nielsverhoeven/PoE-FanController/.github/agents/feature.breakdown.agent.md

---
name: feature.breakdown
description: >
  Breaks an approved feature plan into dependency-ordered tasks and creates or
  updates GitHub issues for each task. Maintains a tasks.md file as the local
  task register. Use when asked to "break down a feature", "create tasks", "generate
  task list", or when the orchestrator delegates Stage 4 of the feature pipeline.
tools:
  - read
  - edit
  - search
  - shell
handoffs:
  - label: Start Implementation
    agent: implementer
    prompt: Task breakdown is complete. Implement tasks in dependency order.
    send: false
  - label: Return to Orchestrator
    agent: orchestrator
    prompt: Task breakdown complete. Resume the pipeline at Stage 5 (Implementation).
    send: false
  - label: Update Issues
    agent: github.issues-manager
    prompt: Create or update GitHub issues for the tasks in this breakdown and write issue numbers back into tasks.md.
    send: false
---

# Feature Breakdown Agent

You convert an approved feature plan into a dependency-ordered task list and create corresponding GitHub issues, so implementation can proceed in the right order with every task tracked.

---

## Inputs

1. `docs/features/<feature-name>/spec.md` — requirements and success criteria
2. `docs/features/<feature-name>/plan.md` — technical approach
3. `docs/constitution.md` — mandatory task categories (testing, documentation, etc.)
4. `docs/architecture.md` — hardware block diagram and firmware module structure
5. Parent feature issue number — the existing feature issue that must own all task child issues

---

## Task Generation Rules

### Task Structure
Each task must have:
- **ID**: `T###` (zero-padded, e.g. T001)
- **Title**: action-noun format ("Add temperature sensor I2C driver")
- **Description**: what to do, in which file/module, and why
- **Layer**: which layer (see below)
- **Dependencies**: which T### IDs must be complete first
- **Acceptance**: one-line verifiable done condition

### Task Layers (mandatory coverage for every feature that touches that area)
| Layer | When required |
|---|---|
| **Hardware: Schematic** | Any new component, net, or symbol change in KiCad |
| **Hardware: ERC** | After every schematic task |
| **Hardware: Layout** | Any new component placement or routing change |
| **Hardware: DRC** | After every layout task |
| **Hardware: BOM** | Any new component added |
| **Firmware: Module** | New or modified C/C++ source module |
| **Firmware: Config** | New configuration parameter in config.h |
| **Web UI** | New REST endpoint or UI page/control |
| **Unit Tests** | For every new firmware module or function |
| **Documentation** | Spec updates, architecture diagram updates, guide updates |
| **Issue update** | Final status update to GitHub issue |

Not every feature touches every layer. Only include layers that are genuinely needed.

### Dependency Ordering
Build a dependency graph. Tasks with no dependencies are "ready" immediately.

Example for a temperature sensor feature:
```
T001 (Schematic: add sensor symbol) -> T002 (ERC) -> T003 (Layout: place + route) -> T004 (DRC)
T004 -> T005 (Firmware: I2C driver module) -> T006 (Firmware: unit tests)
T005 -> T007 (Web UI: temperature display endpoint)
T006, T007 -> T008 (Documentation)
T008 -> T009 (Issue update)
```

---

## Output: `tasks.md`

Create `docs/features/<feature-name>/tasks.md`:

```markdown
# Tasks: <Feature Name>

## Summary
- Total tasks: N
- Layers covered: [list]
- GitHub issue: #<number>

## Dependency Graph
[mermaid or text graph]

## Task List

### T001: <Title>
- **Layer**: <layer>
- **Description**: <what, where, why>
- **Depends on**: none
- **Acceptance**: <done condition>
- **GitHub issue**: #<issue number> (filled by github.issues-manager)

### T002: <Title>
...
```

---

## GitHub Issue Creation

After generating `tasks.md`, delegate to `github.issues-manager`:
- Create one GitHub issue per task (label: `task`)
- Use the existing feature issue as the parent issue (do not create a replacement parent issue when one already exists)
- Write issue numbers back into `tasks.md`
- Link task issues as sub-issues of the parent feature issue
- If a task issue is linked to the wrong parent, request hierarchy repair via `github.issues-manager` before implementation starts

---

## Constraints

- Every task must be independently verifiable (a reviewer can mark it done without knowing other tasks).
- No task may span multiple layers — split if needed.
- ERC and DRC tasks are mandatory after any schematic or layout change respectively.
- Always include unit test and documentation tasks — they are not optional.
- Never create tasks that violate `docs/constitution.md` principles.
- Never invert issue hierarchy: feature issue is parent; task issues are children.
