nielsverhoeven/PoE-FanController/docs/kb/ESP32-P4-POE-ETH/pin-layout.md

# ESP32-P4-ETH Dev Board — Pin Layout Reference

**Board**: Waveshare ESP32-P4-ETH  
**Source**: Board silkscreen image `ESP32-P4-ETH-details-inter-d78f8087f1a1597badd3a1d077c4c057.webp`  
**Verified by user**: Pin 1 = DP/GPIO25, Pin 21 = GPIO48, Pin 3 = GND, Pin 23 = GND

## CRITICAL: Pin Numbering Convention

The board uses a **consecutive (non-Pico) pin layout**:

```
LEFT COLUMN:  Pin  1 (bottom-left)  →  Pin 20 (top-left)
RIGHT COLUMN: Pin 21 (bottom-right) →  Pin 40 (top-right)
```

**Never use Pico-style (dual-row interleaved) numbering for this board.**

### KiCad schematic symbol orientation

The `Custom:J8_Waveshare` symbol in the schematic is oriented to **match the physical board**:
- `pins_right` list runs **40 → 21** (top-to-bottom in symbol) so pin 40 (VBUS) appears at the **top-right** and pin 21 (GPIO48) at the **bottom-right**
- `pins_left` list runs **20 → 1** (top-to-bottom in symbol) so pin 20 (GPIO54) appears at the **top-left** and pin 1 (DP/GPIO25) at the **bottom-left**

This matches the physical Waveshare board where VBUS is at the top-right corner and GPIO48 is at the bottom-right corner.

---

## Left Column — Pins 1–20

| Pin | Signal | Type | Notes |
|-----|---|---|---|
|  1  | DP / GPIO25 | GPIO | USB D+ / General IO |
|  2  | DM / GPIO24 | GPIO | USB D- / General IO |
|  3  | GND | Ground | |
|  4  | SDA / GPIO7 | GPIO | I²C Data |
|  5  | SCL / GPIO8 | GPIO | I²C Clock |
|  6  | GPIO2 | GPIO | |
|  7  | GPIO3 | GPIO | |
|  8  | GND | Ground | |
|  9  | GPIO4 | GPIO | |
| 10  | GPIO5 | GPIO | |
| 11  | GPIO6 | GPIO | |
| 12  | GPIO14 | GPIO | |
| 13  | GND | Ground | |
| 14  | GPIO15 | GPIO | |
| 15  | GPIO16 | GPIO | |
| 16  | GPIO17 | GPIO | |
| 17  | GPIO18 | GPIO | |
| 18  | GND | Ground | |
| 19  | GPIO19 | GPIO | |
| 20  | GPIO54 | GPIO | |

---

## Right Column — Pins 21–40

| Pin | Signal | Type | Notes |
|-----|---|---|---|
| 21  | GPIO48 | GPIO | |
| 22  | GPIO47 | GPIO | |
| 23  | GND | Ground | |
| 24  | GPIO46 | GPIO | |
| 25  | GPIO33 | GPIO | |
| 26  | GPIO32 | GPIO | |
| 27  | GPIO27 | GPIO | |
| 28  | GND | Ground | |
| 29  | GPIO26 | GPIO | |
| 30  | RUN | System Control | Chip enable / run control |
| 31  | GPIO23 | GPIO | |
| 32  | GPIO22 | GPIO | |
| 33  | GND | Ground | |
| 34  | GPIO21 | GPIO | |
| 35  | GPIO20 | GPIO | |
| 36  | 3V3 | Power | 3.3 V output |
| 37  | EN | System Control | Module enable |
| 38  | GND | Ground | |
| 39  | VSYS | Power | System voltage input |
| 40  | VBUS | Power | USB 5 V — **use for 5 V supply** |

---

## Additional Connectors

### USB-C (top of board, labelled on silkscreen)
| Label | Signal |
|---|---|
| D- | USB D- |
| VCC | Power  |
| D+ | USB D+ |
| GND | Ground |

### PoE / ETH Pads (bottom of board)
| Side  | Label | Type | Notes |
|---|---|---|---|
| Left  | GND | Ground | |
| Left  | VCC | Power | |
| Left  | RJ12  | ETH POE  | PoE rail |
| Right | RJ78  | ETH POE  | PoE rail |
| Right | RJ45  | ETH POE  | PoE rail |
| Right | RJ36  | ETH POE  | PoE rail |

---

## Power Supply Notes

- **5 V supply → use Pin 40 (VBUS)**, not Pin 39 (VSYS).  
  VBUS is the USB 5 V bus rail and is the correct source for regulated 5 V.  
  VSYS is the system input rail and should not be used as a 5 V supply source.
- **3.3 V output → Pin 36 (3V3)**. Do not use this as a power input.
- GND pins: 3, 8, 13, 18, 23, 28, 33, 38 (8 total across both columns).

---

## Pin Type Legend

| Colour in image | Meaning |
|---|---|
| Green | GPIO |
| Black | Ground |
| Red | Power |
| Pink | System Control |
| Yellow | ETH POE |

---

## Daughter Board Signal Assignments (PoE FanController PCB)

### Right Column (Pins 21–40) — Fan + Power signals

| Pin | GPIO | Signal | Direction | Connected to |
|-----|---|---|---|---|
| 21  | GPIO48 | **FAN4_PWM**  | Output | J5 pin 4, via D5/R12 PWM LED |
| 22  | GPIO47 | **FAN4_TACH** | Input  | R8 TACH pull-up (10kΩ to +3V3) |
| 23  | GND | GND | — | — |
| 24  | GPIO46 | **FAN3_PWM**  | Output | J4 pin 4, via D4/R11 PWM LED |
| 25  | GPIO33 | **FAN3_TACH** | Input  | R7 TACH pull-up (10kΩ to +3V3) |
| 26  | GPIO32 | NC | — | EMAC_RXD0 — do not use |
| 27  | GPIO27 | NC | — | — |
| 28  | GND | GND | — | — |
| 29  | GPIO26 | NC | — | — |
| 30  | RUN | NC | — | System control — reserved |
| 31  | GPIO23 | **FAN2_PWM**  | Output | J3 pin 4, via D3/R10 PWM LED |
| 32  | GPIO22 | **FAN2_TACH** | Input  | R6 TACH pull-up (10kΩ to +3V3) |
| 33  | GND | GND | — | — |
| 34  | GPIO21 | **FAN1_PWM**  | Output | J2 pin 4, via D2/R9 PWM LED |
| 35  | GPIO20 | **FAN1_TACH** | Input  | R5 TACH pull-up (10kΩ to +3V3) |
| 36  | +3V3 | **+3V3** | Power  | TACH pull-ups R5-R8, sensor VCC |
| 37  | EN | NC | — | Module enable — reserved |
| 38  | GND | GND | — | — |
| 39  | VSYS | NC | — | Do NOT use for 5V supply |
| 40  | VBUS | **+5V** | Power  | U_BOOST IN+ (5V→12V boost input) |

> ⚠️ PWM and TACH are on **adjacent pins per fan** — PWM on the lower-numbered pin, TACH on the higher. This is the result of a board layout reshuffle (2026-06-14) that required swapping from the original TACH-low/PWM-high order.

### Left Column (Pins 1–20) — Sensor + LED signals

| Pin | GPIO | Signal | Direction | Connected to |
|-----|---|---|---|---|
| 6 | GPIO2  | DS18B20_DATA | Bidirectional | R14 pull-up (4.7kΩ to +3V3), J6 |
| 10  | GPIO5  | DHT11_DATA | Input | HUM1 pin 2 |
| 11  | GPIO6  | PROBE_LED | Output | R15 → LED6 |
| 16  | GPIO17 | PROG_LED | Output | R13 → LED2 |
| 17  | GPIO18 | PWR_LED | Output | R3 → LED1 |
| 3,8,13,18 | GND | GND | — | — |

### PCB Component Positions (as-built, 2026-06-15 — fully routed)

Board outline: **92mm × 78mm** (X: 12–104mm, Y: 12–90mm) with rounded corners.
All signal components on F.Cu. Wire jumpers JP1–JP4 on B.Cu.
Routing: single layer F.Cu, **0.4mm** track width, 242 segments.
**DRC: 0 errors, 0 unconnected, 7 warnings (cosmetic only).**

| Ref | X (mm) | Y (mm) | Rotation | Layer | Role |
|-----|---|---|---|---|---|
| **J8** | **41.000** | **40.770** | **90°** | F.Cu | ESP32-P4-PoE-ETH interface header |
| U_BOOST | 77.000 | 25.140 | 0° | F.Cu | DC-DC boost module (LM2587, 5V→12V) |
| J2 | 96.500 | 46.500 | 180° | F.Cu | FAN1 header (Molex KK-254 4-pin) |
| J3 | 96.500 | 58.500 | 180° | F.Cu | FAN2 header |
| J4 | 96.500 | 70.500 | 180° | F.Cu | FAN3 header |
| J5 | 96.500 | 82.500 | 180° | F.Cu | FAN4 header |
| R5 | 65.000 | 47.770 | 90° | F.Cu | FAN1 TACH pull-up (10kΩ, pin 35/GPIO20) |
| R6 | 65.000 | 60.450 | 90° | F.Cu | FAN2 TACH pull-up (10kΩ, pin 32/GPIO22) |
| R7 | 65.000 | 73.130 | 90° | F.Cu | FAN3 TACH pull-up (10kΩ, pin 25/GPIO33) |
| R8 | 65.000 | 85.810 | 90° | F.Cu | FAN4 TACH pull-up (10kΩ, pin 22/GPIO47) |
| R9 | 69.000 | 40.150 | -90° | F.Cu | FAN1 PWM LED resistor (150Ω) |
| R10 | 69.000 | 52.830 | -90° | F.Cu | FAN2 PWM LED resistor (150Ω) |
| R11 | 69.000 | 65.510 | -90° | F.Cu | FAN3 PWM LED resistor (150Ω) |
| R12 | 69.000 | 78.190 | -90° | F.Cu | FAN4 PWM LED resistor (150Ω) |
| D2 | 77.460 | 46.500 | 0° | F.Cu | FAN1 PWM activity LED |
| D3 | 77.460 | 58.500 | 0° | F.Cu | FAN2 PWM activity LED |
| D4 | 77.460 | 70.500 | 0° | F.Cu | FAN3 PWM activity LED |
| D5 | 77.460 | 82.500 | 0° | F.Cu | FAN4 PWM activity LED |
| **HUM1** | **39.500** | **77.960** | **90°** | F.Cu | DHT22 temperature/humidity sensor |
| J6 | 19.920 | 61.995 | 0° | F.Cu | DS18B20 probe connector |
| JP1 | 33.500 | 68.000 | -90° | B.Cu | Wire jumper |
| JP2 | 60.000 | 35.620 | 90° | B.Cu | Wire jumper |
| JP3 | 60.000 | 55.390 | 90° | B.Cu | Wire jumper |
| JP4 | 60.000 | 70.310 | 90° | B.Cu | Wire jumper |
| LED1 | 18.000 | 30.975 | -90° | F.Cu | Power status LED |
| LED2 | 24.500 | 30.975 | -90° | F.Cu | OTA/prog LED |
| LED6 | 17.975 | 51.475 | -90° | F.Cu | DS18B20 probe LED |
| R3 | 17.975 | 18.475 | -90° | F.Cu | PWR_LED resistor (330Ω) |
| R13 | 24.500 | 18.230 | -90° | F.Cu | PROG_LED resistor (330Ω) |
| R14 | 27.000 | 55.095 | 90° | F.Cu | DS18B20 pull-up (4.7kΩ) |
| R15 | 18.000 | 39.475 | -90° | F.Cu | PROBE_LED resistor (330Ω) |
