nielsverhoeven/PoE-FanController/.github/skills/kikit-pcb-modify/SKILL.md

---
name: kikit-pcb-modify
description: >
  Modify the PoE FanController PCB programmatically using KiCad's Python API
  (pcbnew), available via KiKit's Python environment. Use for surgical PCB
  changes: resizing the board outline, repositioning footprints, adding copper
  zones, or scripted trace routing. Use when asked to 'move component', 'resize
  board', 'reposition footprint', 'update PCB outline', 'script PCB changes',
  'add trace', or 'route trace programmatically'.
allowed-tools: shell
---

## Purpose

Apply targeted, reproducible changes to `PoE-FanController.kicad_pcb` using
the pcbnew Python API, invoked via KiCad's embedded Python interpreter.
This is the only scripted path to PCB edits — the `.kicad_pcb` file is never
auto-generated by `generate_project.py` (P-KI-07).

---

## Environment Constants

```powershell
$kicadPy = "C:\Users\Niels\AppData\Local\Programs\KiCad\10.0\bin\python.exe"
$pcb     = "C:/repos-github/PoE-FanController/hardware/kicad/PoE-FanController.kicad_pcb"
# NOTE: always forward slashes in $pcb — backslashes cause pcbnew unicode errors
```

Verify the Python environment:
```powershell
& $kicadPy -c "import pcbnew; print(pcbnew.GetBuildVersion())"
```

---

## Step 1 — Check Netlist Status (CRITICAL prerequisite)

Before any routing work, verify that net assignments are present in the PCB:

```powershell
& $kicadPy -c "
import sys; sys.path.insert(0, r'C:/Users/Niels/AppData/Local/Programs/KiCad/10.0/bin')
import pcbnew
board = pcbnew.LoadBoard('$pcb')
board.BuildConnectivity()
nets = [str(n) for n in board.GetNetInfo().NetsByName().keys() if n]
print('Nets found:', sorted(nets))
print('Unconnected:', board.GetConnectivity().GetUnconnectedCount(False))
"
```

**If nets list is empty (only GND or blank):**
The netlist has not been imported. You must run **KiCad GUI → Tools → Update PCB
from Schematic (F8)** before any routing is possible. Report this to the user and
stop — do not attempt routing without nets.

**If nets are present:** proceed with modifications.

---

## Step 2 — Script Template

Every PCB modification script follows this pattern:

```python
import sys
sys.path.insert(0, r'C:/Users/Niels/AppData/Local/Programs/KiCad/10.0/bin')
import pcbnew

PCB = 'C:/repos-github/PoE-FanController/hardware/kicad/PoE-FanController.kicad_pcb'
board = pcbnew.LoadBoard(PCB)

def mm(x): return pcbnew.FromMM(x)

# --- Make changes here ---

# ALWAYS end with:
board.BuildConnectivity()
board.Save(PCB)
print("Saved:", PCB)
```

Save as a temporary `.py` file and run:
```powershell
& $kicadPy path\to\script.py
```

---

## Step 3 — Common Operations

### Resize board outline
```python
# Delete all existing Edge.Cuts
for d in list(board.GetDrawings()):
    if d.GetLayer() == pcbnew.Edge_Cuts:
        board.Delete(d)

# Draw new outline (42x78mm portrait — constitution P-HW-04)
seg = pcbnew.PCB_SHAPE(board)
seg.SetShape(pcbnew.SHAPE_T_RECT)
seg.SetStart(pcbnew.VECTOR2I(mm(0), mm(0)))
seg.SetEnd(pcbnew.VECTOR2I(mm(42), mm(78)))
seg.SetLayer(pcbnew.Edge_Cuts)
seg.SetWidth(mm(0.05))
board.Add(seg)
```

### Move a footprint
```python
fp = board.FindFootprintByReference('J8')
if not fp:
    raise ValueError("Footprint J8 not found")
fp.SetPosition(pcbnew.VECTOR2I(mm(10.50), mm(28.80)))
fp.SetOrientationDegrees(90)   # 90° CCW
```

### J8 canonical placement (constitution v3.1.0)
```python
# J8: Custom:PinSocket_2x20_P2.54mm_P15.38mm_Vertical
# Row1 (odd)  → X=2.81mm from left board edge
# Row2 (even) → X=18.19mm from left board edge
# Centre X = (2.81+18.19)/2 = 10.50mm
# First pin at Y=4.67mm, 20 pins × 2.54mm → centre Y=4.67+9.5×2.54=28.80mm
fp = board.FindFootprintByReference('J8')
fp.SetPosition(pcbnew.VECTOR2I(mm(10.50), mm(28.80)))
fp.SetOrientationDegrees(90)
```

### Add a straight copper trace
```python
# Prerequisite: netlist must be imported (Step 1)
track = pcbnew.PCB_TRACK(board)
track.SetLayer(pcbnew.F_Cu)
track.SetWidth(mm(0.25))   # 0.25mm = signal; use 1.0mm for power (+5V, +12V, GND)
track.SetStart(pcbnew.VECTOR2I(mm(x1), mm(y1)))
track.SetEnd(pcbnew.VECTOR2I(mm(x2), mm(y2)))
net = board.FindNet('NET_NAME')   # e.g. 'FAN1_PWM', '+5V', 'GND'
if net is None:
    raise ValueError("Net not found — run Update PCB from Schematic (F8) first")
track.SetNet(net)
board.Add(track)
```

### Add a copper pour zone
```python
zone = pcbnew.ZONE(board)
zone.SetLayer(pcbnew.F_Cu)
zone.SetNet(board.FindNet('GND'))
zone.SetIsRuleArea(False)
outline = zone.Outline()
outline.NewOutline()
outline.Append(mm(0), mm(0))
outline.Append(mm(42), mm(0))
outline.Append(mm(42), mm(78))
outline.Append(mm(0), mm(78))
board.Add(zone)
filler = pcbnew.ZONE_FILLER(board)
filler.Fill(board.Zones())
```

### List all footprints and their positions
```python
for fp in board.GetFootprints():
    pos = fp.GetPosition()
    print(f"{fp.GetReference():8} at ({pcbnew.ToMM(pos.x):.2f}, {pcbnew.ToMM(pos.y):.2f})mm  rot={fp.GetOrientationDegrees():.0f}°")
```

---

## Step 4 — Track widths (per constitution P-HW-07)

| Net class | Width | Use for |
|---|---|---|
| Signal | `mm(0.25)` | PWM, TACH, NTC_ADC, STATUS_LED |
| Power | `mm(1.0)` | +5V, +12V, GND |

---

## Step 5 — Run DRC After Changes

```powershell
$kicadCli = "C:\Users\Niels\AppData\Local\Programs\KiCad\10.0\bin\kicad-cli.exe"
& $kicadCli pcb drc `
  --output hardware/kicad/drc_result.rpt `
  hardware/kicad/PoE-FanController.kicad_pcb 2>&1 | Select-Object -Last 5
```

Target: 0 errors, 0 unconnected. Up to 5 silk warnings are acceptable.
If violations exceed the baseline, investigate and fix before committing.

---

## Step 6 — Commit

```powershell
cd C:\repos-github\PoE-FanController
git add hardware/kicad/PoE-FanController.kicad_pcb
git add hardware/kicad/drc_result.rpt
git commit -m "hw(pcb): <describe change>

DRC: <N> silk warnings, 0 errors, 0 unconnected.

Co-authored-by: Copilot <223556219+Copilot@users.noreply.github.com>"
git push origin feature/75-esp32-p4-poe-eth-daughterboard
```

---

## Quality Rules

- **Forward slashes only** in PCB file paths passed to pcbnew — backslashes cause
  unicode errors inside the KiCad Python runtime.
- **Always call `board.BuildConnectivity()` before `board.Save()`** — skip this
  and the saved file may have broken ratsnest data.
- **Never modify `PoE-FanController.kicad_sch`** — it is auto-generated by
  `python hardware/generate_project.py` (P-KI-04). Only edit `.kicad_pcb`.
- **Check for nets before routing** — if `board.FindNet('X')` returns None, the
  netlist hasn't been imported. Routing without nets creates unassigned traces.
- After every modification, run DRC and report the violation count to the user.
- Clean up any temporary `.py` scripts after the operation completes.
