nielsverhoeven/PoE-FanController/docs/features/schematic-readability/plan.md

# Technical Plan: SCH — Improve Schematic Readability to Match DMX_NODE Reference Style

**GitHub Issue:** #25 — "SCH: improve schematic readability to match DMX_NODE reference style"
**Branch:** `feature/25-schematic-readability`
**Merged via:** PR #24 (core implementation complete on `main`)
**Status:** Implementation complete; this document records decisions, acceptance criteria, and remaining gaps
**Date:** 2026-06-06

---

## 1. Overview

The PoE FanController schematic is produced entirely by `hardware/generate_project.py` — manual edits to
the `.kicad_sch` file are forbidden (P-HW-05, P-KI-04). Issue #25 tasked the team with closing the gap
between the generated schematic and the KiCad 10 best-practice patterns demonstrated by the reference
project at `docs/reference-samples/DMX_NODE/DMX_NODE.kicad_sch`.

The core implementation was delivered in PR #24 (commit `6e7d1b1`). This plan documents:

- What was implemented and where in the generator (§2)
- The technical decisions behind each change (§3)
- Acceptance criteria a tester can verify without opening Python (§4)
- Remaining gaps not addressed by PR #24 (§5)
- Constitution compliance mapping (§6)

---

## 2. Architecture Fit

### 2.1 Schematic Block Layout (A2 sheet)

| Block | x range (mm) | y range (mm) | Section header |
|---|---|---|---|
| PoE Power Input | 25–110 | 30–100 | ✅ Blue bold 2.54 mm |
| 3.3V Regulator | 25–145 | 110–185 | ✅ Blue bold 2.54 mm |
| ESP32-WROOM-32 | 155–295 | 30–210 | ✅ Blue bold 2.54 mm |
| Fan Headers (4×) | 305–420 | 30–200 | ✅ Blue bold 2.54 mm |
| USB / UART Bridge | 25–195 | 215–385 | ✅ Blue bold 2.54 mm |

The isolation barrier at x = 38 mm (P-ISO-02) bisects the PoE Input block. J1 (x ≈ 38 mm) sits on
the barrier; U1 Ag9905M (x ≈ 97 mm) sits to the right, on the secondary (SELV) side of the isolation
domain boundary. `GND_PRI` is connected only to U1 pin 6 (VOUT_N) and has no connections to `GND`.

### 2.2 Signal Classification

Per P-SCH-01, every signal crossing two functional blocks must use `global_label`. The table below
shows every net in the schematic and its correct label type:

| Net(s) | Crosses blocks? | Correct type | Implemented |
|---|---|---|---|
| `FAN1_PWM` … `FAN4_PWM` | ESP32 ↔ Fan Headers | `global_label` | ✅ |
| `FAN1_TACH` … `FAN4_TACH` | ESP32 ↔ Fan Headers | `global_label` | ✅ |
| `ESP_EN` | ESP32 ↔ USB/UART Bridge | `global_label` | ✅ |
| `BOOT` | ESP32 ↔ USB/UART Bridge | `global_label` | ✅ |
| `ESP_TX` | ESP32 ↔ USB/UART Bridge | `global_label` | ✅ |
| `ESP_RX` | ESP32 ↔ USB/UART Bridge | `global_label` | ✅ |
| `USB_DP` | USB/UART Bridge (J6 ↔ U4) | `global_label` | ✅ |
| `USB_DN` | USB/UART Bridge (J6 ↔ U4) | `global_label` | ✅ |
| `POE_A+`, `POE_A-`, `POE_B+`, `POE_B-` | Intra-block (J1 and U1 both in PoE Input block) | `label` ✅ | ✅ |
| `+3V3_SW` | Intra-block (3.3V Regulator) | `label` ✅ | ✅ |
| `GPIO2` | Intra-block (ESP32 block: U3 IO2 → R3) | `label` ✅ | ✅ |
| `LED_A` | Intra-block (ESP32 block: R3 → LED1) | `label` ✅ | ✅ |
| `CH340_V3` | Intra-block (USB/UART Bridge: U4 V3 → C7) | `label` ✅ | ✅ |
| `CC1`, `CC2` | Intra-block (USB/UART Bridge: J6 → R9/R10) | `label` ✅ | ✅ |
| `NTC_ADC` | Intra-block (ESP32 block: U3 IO32 → R4/NTC1) | `global_label` | ✅ Fixed in T002 — all three endpoints use `global_label` |

---

## 3. Implementation: What Was Done and Why
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
