nielsverhoeven/PoE-FanController/docs/features/schematic-readability/tasks.md

# Tasks: SCH — Improve Schematic Readability to Match DMX_NODE Reference Style

## Summary

- **Total tasks:** 5
- **Layers covered:** Hardware: ERC, Hardware: Schematic (generator), Documentation, Issue update
- **GitHub parent issue:** #25
- **Branch:** `feature/25-schematic-readability`
- **Core implementation status:** Complete (merged via PR #24 into `main`)
- **Remaining scope:** Two gaps identified post-merge; all other acceptance criteria already satisfied on `main`
- **T001:** ✅ Complete (commit `bd6c99c`) — erc_output.json regenerated as valid JSON, 0 errors
- **T002:** ✅ Complete (commit `599edfd`) — NTC_ADC global_label shapes fixed in generator and schematic
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
