nielsverhoeven/PoE-FanController/docs/kb/PoE_FanController.drawio.png

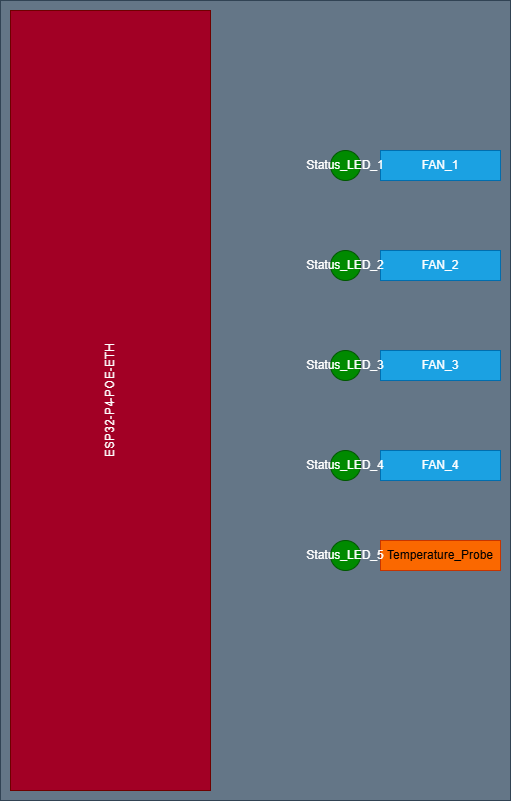
docs/kb/PoE_FanController.drawio.png
