nielsverhoeven/PoE-FanController/firmware/test/test_pins/test_pins.cpp

/**
 * @file test_pins.cpp
 * @brief Unit tests: GPIO pin constant correctness and collision check.
 *
 * Verifies all 13 GPIO constants from architecture.md §4 match expected values,
 * and that no two functions share the same GPIO number.
 *
 * Run: pio test -e native
 */
#include <unity.h>
#include "pins.h"

// ---------------------------------------------------------------------------
// Individual constant checks
// ---------------------------------------------------------------------------
void test_fan_pwm_pins()
{
    TEST_ASSERT_EQUAL(20, FAN1_PWM_PIN);
    TEST_ASSERT_EQUAL(22, FAN2_PWM_PIN);
    TEST_ASSERT_EQUAL(33, FAN3_PWM_PIN);
    TEST_ASSERT_EQUAL(47, FAN4_PWM_PIN);
}

void test_fan_tach_pins()
{
    TEST_ASSERT_EQUAL(21, FAN1_TACH_PIN);
    TEST_ASSERT_EQUAL(23, FAN2_TACH_PIN);
    TEST_ASSERT_EQUAL(46, FAN3_TACH_PIN);
    TEST_ASSERT_EQUAL(48, FAN4_TACH_PIN);
}

void test_adc_and_misc_pins()
{
    TEST_ASSERT_EQUAL(5,  DHT11_DATA_PIN);
    TEST_ASSERT_EQUAL(2,  STATUS_LED_PIN);
    TEST_ASSERT_EQUAL(15, PROG_LED_PIN);
    TEST_ASSERT_EQUAL(0,  BOOT_PIN);
}

void test_eth_management_pins()
{
    TEST_ASSERT_EQUAL(52, ETH_MDIO_PIN);
    TEST_ASSERT_EQUAL(31, ETH_MDC_PIN);
    TEST_ASSERT_EQUAL(51, ETH_PHY_RST_PIN);
}

// ---------------------------------------------------------------------------
// No-collision check: all 13 defined pins must be unique
// ---------------------------------------------------------------------------
void test_no_gpio_collisions()
{
    const int pins[] = {
        FAN1_PWM_PIN,  FAN2_PWM_PIN,  FAN3_PWM_PIN,  FAN4_PWM_PIN,
        FAN1_TACH_PIN, FAN2_TACH_PIN, FAN3_TACH_PIN, FAN4_TACH_PIN,
        DHT11_DATA_PIN, STATUS_LED_PIN, PROG_LED_PIN,  BOOT_PIN,
        ETH_MDIO_PIN,  ETH_MDC_PIN,   ETH_PHY_RST_PIN,
        DS18B20_DATA_PIN, PROBE_LED_PIN,
    };
    const int N = sizeof(pins) / sizeof(pins[0]);

    for (int i = 0; i < N; i++) {
        for (int j = i + 1; j < N; j++) {
            TEST_ASSERT_NOT_EQUAL_MESSAGE(pins[i], pins[j],
                "GPIO collision detected between two pin constants");
        }
    }
}

// ---------------------------------------------------------------------------
// RMII forbidden zone: none of the defined pins may fall in GPIO32-37 or GPIO50
// (those are fixed RMII pins, must never be reassigned)
// ---------------------------------------------------------------------------
void test_no_rmii_collision()
{
    const int rmii_fixed[] = { 32, 33, 34, 35, 36, 37, 50 };
    const int user_pins[]  = {
        FAN1_PWM_PIN,  FAN2_PWM_PIN,  FAN3_PWM_PIN,  FAN4_PWM_PIN,
        FAN1_TACH_PIN, FAN2_TACH_PIN, FAN3_TACH_PIN, FAN4_TACH_PIN,
        DHT11_DATA_PIN, STATUS_LED_PIN, PROG_LED_PIN,  BOOT_PIN,
        ETH_MDIO_PIN,  ETH_MDC_PIN,   ETH_PHY_RST_PIN,
        DS18B20_DATA_PIN, PROBE_LED_PIN,
    };

    for (int u = 0; u < (int)(sizeof(user_pins)/sizeof(user_pins[0])); u++) {
        for (int r = 0; r < (int)(sizeof(rmii_fixed)/sizeof(rmii_fixed[0])); r++) {
            TEST_ASSERT_NOT_EQUAL_MESSAGE(user_pins[u], rmii_fixed[r],
                "User GPIO conflicts with RMII fixed IO_MUX pin");
        }
    }
}

// ---------------------------------------------------------------------------
// DS18B20 probe pin checks — GPIO19 / GPIO6
// ---------------------------------------------------------------------------
void test_gpio19_no_conflict()
{
    // GPIO19 (DS18B20_DATA_PIN) must not equal any existing pin constant
    const int existing[] = {
        FAN1_PWM_PIN,  FAN2_PWM_PIN,  FAN3_PWM_PIN,  FAN4_PWM_PIN,
        FAN1_TACH_PIN, FAN2_TACH_PIN, FAN3_TACH_PIN, FAN4_TACH_PIN,
        DHT11_DATA_PIN, STATUS_LED_PIN, PROG_LED_PIN,  BOOT_PIN,
        ETH_MDIO_PIN,  ETH_MDC_PIN,   ETH_PHY_RST_PIN,
    };
    for (int i = 0; i < (int)(sizeof(existing)/sizeof(existing[0])); i++) {
        TEST_ASSERT_NOT_EQUAL_MESSAGE(DS18B20_DATA_PIN, existing[i],
            "GPIO19 (DS18B20_DATA_PIN) conflicts with existing pin constant");
    }
}

void test_probe_led_no_conflict()
{
    // GPIO6 (PROBE_LED_PIN) must not equal any existing pin constant
    const int existing[] = {
        FAN1_PWM_PIN,  FAN2_PWM_PIN,  FAN3_PWM_PIN,  FAN4_PWM_PIN,
        FAN1_TACH_PIN, FAN2_TACH_PIN, FAN3_TACH_PIN, FAN4_TACH_PIN,
        DHT11_DATA_PIN, STATUS_LED_PIN, PROG_LED_PIN,  BOOT_PIN,
        ETH_MDIO_PIN,  ETH_MDC_PIN,   ETH_PHY_RST_PIN,
    };
    for (int i = 0; i < (int)(sizeof(existing)/sizeof(existing[0])); i++) {
        TEST_ASSERT_NOT_EQUAL_MESSAGE(PROBE_LED_PIN, existing[i],
            "GPIO6 (PROBE_LED_PIN) conflicts with existing pin constant");
    }
}

void test_ds18b20_probe_led_distinct()
{
    TEST_ASSERT_NOT_EQUAL_MESSAGE(DS18B20_DATA_PIN, PROBE_LED_PIN,
        "DS18B20_DATA_PIN (GPIO19) and PROBE_LED_PIN (GPIO6) must be distinct");
}

// ---------------------------------------------------------------------------
// PWM parameter checks
// ---------------------------------------------------------------------------
void test_fan_pwm_params()
{
    TEST_ASSERT_EQUAL(25000, FAN_PWM_FREQ_HZ);
    TEST_ASSERT_EQUAL(8,     FAN_PWM_RESOLUTION);
    TEST_ASSERT_EQUAL(255,   FAN_PWM_SAFE_DEFAULT);
}

// ---------------------------------------------------------------------------
// Runner
// ---------------------------------------------------------------------------
void setUp()    {}
void tearDown() {}

int main(int argc, char** argv)
{
    UNITY_BEGIN();

    RUN_TEST(test_fan_pwm_pins);
    RUN_TEST(test_fan_tach_pins);
    RUN_TEST(test_adc_and_misc_pins);
    RUN_TEST(test_eth_management_pins);
    RUN_TEST(test_no_gpio_collisions);
    RUN_TEST(test_no_rmii_collision);
    RUN_TEST(test_fan_pwm_params);
    RUN_TEST(test_gpio19_no_conflict);
    RUN_TEST(test_probe_led_no_conflict);
    RUN_TEST(test_ds18b20_probe_led_distinct);

    return UNITY_END();
}
