nielsverhoeven/PoE-FanController/hardware/generator/pcb_utils.py

"""
pcb_utils.py — PCB utility helpers for the PoE FanController generator.

Placeholder module expected by the CI syntax-check gate.
Actual PCB manipulation is performed by import_netlist.py and fix_placement.py
using the pcbnew API directly.
"""
